RetroNynjah/C128-character-ROM-adapter/rev1/kicad schematics/CharRom adapter Rev1.kicad_sch

## KiCad design rev1/kicad schematics/CharRom adapter Rev1.kicad_sch (2024-04-05)

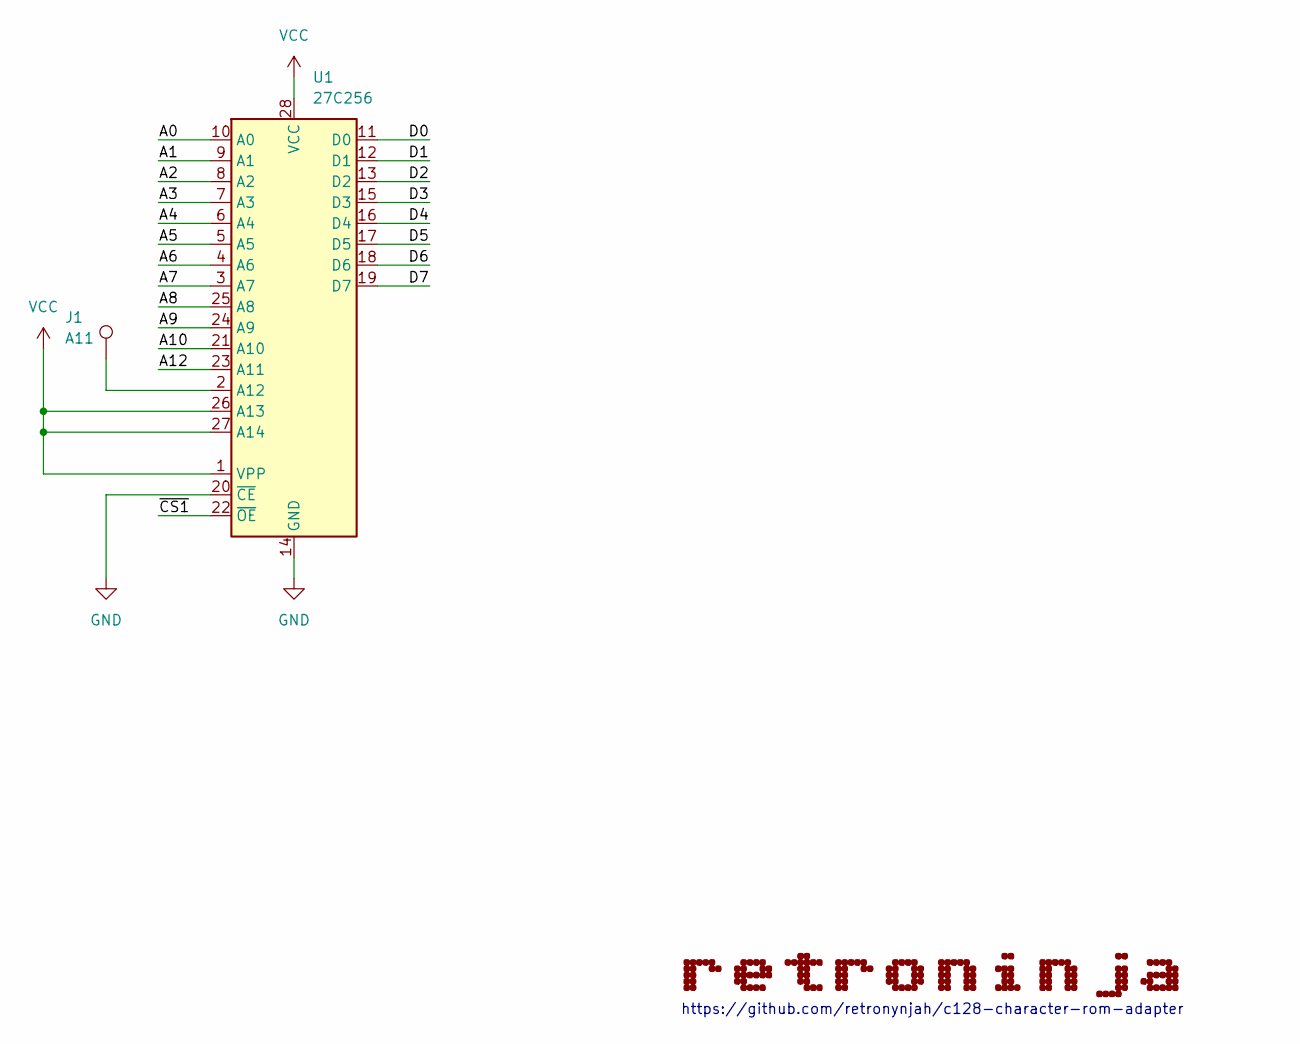
[picture p6: schematic CharRom adapter Rev1.kicad_sch]

Parts:
J1: A11; TestPoint_THTPad_D2.0mm_Drill1.0mm
U1: 27C256; DIP-28_W15.24mm

Connections:
A0: U1.10 (A0)
A1: U1.9 (A1)
A2: U1.8 (A2)
A3: U1.7 (A3)
A4: U1.6 (A4)
A5: U1.5 (A5)
A6: U1.4 (A6)
A7: U1.3 (A7)
A8: U1.25 (A8)
A9: U1.24 (A9)
A10: U1.21 (A10)
A12: U1.23 (A11)
D0: U1.11 (D0)
D1: U1.12 (D1)
D2: U1.13 (D2)
D3: U1.15 (D3)
D4: U1.16 (D4)
D5: U1.17 (D5)
D6: U1.18 (D6)
D7: U1.19 (D7)
GND: U1.14 (GND), U1.20 (~CE)
unnamed: J1.1, U1.2 (A12)
VCC: U1.1 (VPP), U1.26 (A13), U1.27 (A14), U1.28 (VCC)
~CS1: U1.22 (~OE)

Notes on the sheet:
https://github.com/retronynjah/c128-character-rom-adapter
